Brandochili/Easy-Shot/20240221_093328.jpg

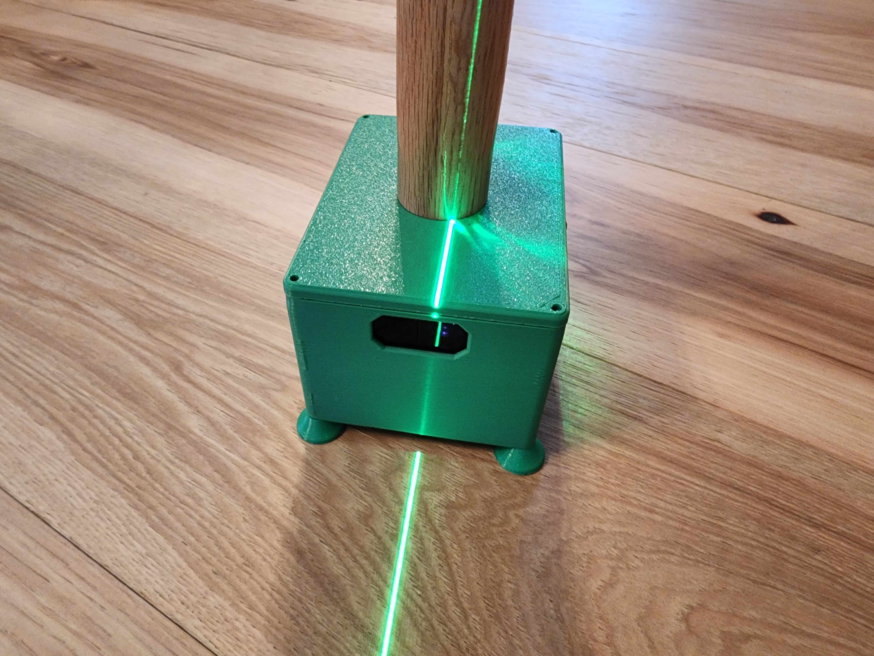
20240221_093328.jpg
