Brandochili/Easy-Shot/20240221_093351.jpg

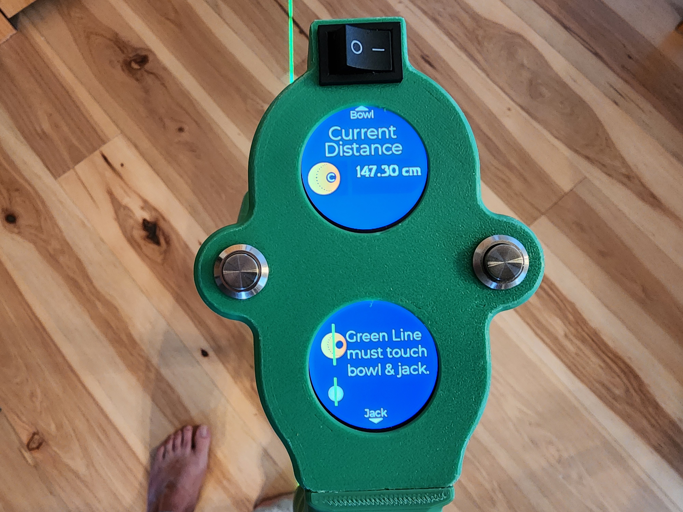
20240221_093351.jpg
