Brandochili/Easy-Shot/dial.h

const uint8_t dial[] PROGMEM = {
0xFF, 0xD8, 0xFF, 0xE0, 0x00, 0x10, 0x4A, 0x46, 0x49, 0x46, 0x00, 0x01, 0x02, 0x01, 0x00, 0x48, 
0x00, 0x48, 0x00, 0x00, 0xFF, 0xED, 0x00, 0x2C, 0x50, 0x68, 0x6F, 0x74, 0x6F, 0x73, 0x68, 0x6F, 
0x70, 0x20, 0x33, 0x2E, 0x30, 0x00, 0x38, 0x42, 0x49, 0x4D, 0x03, 0xED, 0x00, 0x00, 0x00, 0x00, 
0x00, 0x10, 0x00, 0x48, 0x00, 0x00, 0x00, 0x01, 0x00, 0x01, 0x00, 0x48, 0x00, 0x00, 0x00, 0x01, 
0x00, 0x01, 0xFF, 0xE1, 0x7E, 0xFE, 0x68, 0x74, 0x74, 0x70, 0x3A, 0x2F, 0x2F, 0x6E, 0x73, 0x2E, 
0x61, 0x64, 0x6F, 0x62, 0x65, 0x2E, 0x63, 0x6F, 0x6D, 0x2F, 0x78, 0x61, 0x70, 0x2F, 0x31, 0x2E, 
0x30, 0x2F, 0x00, 0x3C, 0x3F, 0x78, 0x70, 0x61, 0x63, 0x6B, 0x65, 0x74, 0x20, 0x62, 0x65, 0x67, 
0x69, 0x6E, 0x3D, 0x22, 0xEF, 0xBB, 0xBF, 0x22, 0x20, 0x69, 0x64, 0x3D, 0x22, 0x57, 0x35, 0x4D, 
0x30, 0x4D, 0x70, 0x43, 0x65, 0x68, 0x69, 0x48, 0x7A, 0x72, 0x65, 0x53, 0x7A, 0x4E, 0x54, 0x63, 
0x7A, 0x6B, 0x63, 0x39, 0x64, 0x22, 0x3F, 0x3E, 0x0A, 0x3C, 0x78, 0x3A, 0x78, 0x6D, 0x70, 0x6D, 
0x65, 0x74, 0x61, 0x20, 0x78, 0x6D, 0x6C, 0x6E, 0x73, 0x3A, 0x78, 0x3D, 0x22, 0x61, 0x64, 0x6F, 
0x62, 0x65, 0x3A, 0x6E, 0x73, 0x3A, 0x6D, 0x65, 0x74, 0x61, 0x2F, 0x22, 0x20, 0x78, 0x3A, 0x78, 
0x6D, 0x70, 0x74, 0x6B, 0x3D, 0x22, 0x41, 0x64, 0x6F, 0x62, 0x65, 0x20, 0x58, 0x4D, 0x50, 0x20, 
0x43, 0x6F, 0x72, 0x65, 0x20, 0x39, 0x2E, 0x30, 0x2D, 0x63, 0x30, 0x30, 0x31, 0x20, 0x37, 0x39, 
0x2E, 0x31, 0x34, 0x65, 0x63, 0x62, 0x34, 0x32, 0x2C, 0x20, 0x32, 0x30, 0x32, 0x32, 0x2F, 0x31, 
0x32, 0x2F, 0x30, 0x32, 0x2D, 0x31, 0x39, 0x3A, 0x31, 0x32, 0x3A, 0x34, 0x34, 0x20, 0x20, 0x20, 
0x20, 0x20, 0x20, 0x20, 0x20, 0x22, 0x3E, 0x0A, 0x20, 0x20, 0x20, 0x3C, 0x72, 0x64, 0x66, 0x3A, 
0x52, 0x44, 0x46, 0x20, 0x78, 0x6D, 0x6C, 0x6E, 0x73, 0x3A, 0x72, 0x64, 0x66, 0x3D, 0x22, 0x68, 
0x74, 0x74, 0x70, 0x3A, 0x2F, 0x2F, 0x77, 0x77, 0x77, 0x2E, 0x77, 0x33, 0x2E, 0x6F, 0x72, 0x67, 
0x2F, 0x31, 0x39, 0x39, 0x39, 0x2F, 0x30, 0x32, 0x2F, 0x32, 0x32, 0x2D, 0x72, 0x64, 0x66, 0x2D, 
0x73, 0x79, 0x6E, 0x74, 0x61, 0x78, 0x2D, 0x6E, 0x73, 0x23, 0x22, 0x3E, 0x0A, 0x20, 0x20, 0x20, 
0x20, 0x20, 0x20, 0x3C, 0x72, 0x64, 0x66, 0x3A, 0x44, 0x65, 0x73, 0x63, 0x72, 0x69, 0x70, 0x74, 
0x69, 0x6F, 0x6E, 0x20, 0x72, 0x64, 0x66, 0x3A, 0x61, 0x62, 0x6F, 0x75, 0x74, 0x3D, 0x22, 0x22, 
0x0A, 0x20, 0x20, 0x20, 0x20, 0x20, 0x20, 0x20, 0x20, 0x20, 0x20, 0x20, 0x20, 0x78, 0x6D, 0x6C, 
0x6E, 0x73, 0x3A, 0x64, 0x63, 0x3D, 0x22, 0x68, 0x74, 0x74, 0x70, 0x3A, 0x2F, 0x2F, 0x70, 0x75, 
0x72, 0x6C, 0x2E, 0x6F, 0x72, 0x67, 0x2F, 0x64, 0x63, 0x2F, 0x65, 0x6C, 0x65, 0x6D, 0x65, 0x6E, 
0x74, 0x73, 0x2F, 0x31, 0x2E, 0x31, 0x2F, 0x22, 0x0A, 0x20, 0x20, 0x20, 0x20, 0x20, 0x20, 0x20, 
0x20, 0x20, 0x20, 0x20, 0x20, 0x78, 0x6D, 0x6C, 0x6E, 0x73, 0x3A, 0x78, 0x6D, 0x70, 0x3D, 0x22, 
0x68, 0x74, 0x74, 0x70, 0x3A, 0x2F, 0x2F, 0x6E, 0x73, 0x2E, 0x61, 0x64, 0x6F, 0x62, 0x65, 0x2E, 
0x63, 0x6F, 0x6D, 0x2F, 0x78, 0x61, 0x70, 0x2F, 0x31, 0x2E, 0x30, 0x2F, 0x22, 0x0A, 0x20, 0x20, 
0x20, 0x20, 0x20, 0x20, 0x20, 0x20, 0x20, 0x20, 0x20, 0x20, 0x78, 0x6D, 0x6C, 0x6E, 0x73, 0x3A, 
0x78, 0x6D, 0x70, 0x47, 0x49, 0x6D, 0x67, 0x3D, 0x22, 0x68, 0x74, 0x74, 0x70, 0x3A, 0x2F, 0x2F, 
0x6E, 0x73, 0x2E, 0x61, 0x64, 0x6F, 0x62, 0x65, 0x2E, 0x63, 0x6F, 0x6D, 0x2F, 0x78, 0x61, 0x70, 
0x2F, 0x31, 0x2E, 0x30, 0x2F, 0x67, 0x2F, 0x69, 0x6D, 0x67, 0x2F, 0x22, 0x0A, 0x20, 0x20, 0x20, 
0x20, 0x20, 0x20, 0x20, 0x20, 0x20, 0x20, 0x20, 0x20, 0x78, 0x6D, 0x6C, 0x6E, 0x73, 0x3A, 0x78, 
0x6D, 0x70, 0x4D, 0x4D, 0x3D, 0x22, 0x68, 0x74, 0x74, 0x70, 0x3A, 0x2F, 0x2F, 0x6E, 0x73, 0x2E, 
0x61, 0x64, 0x6F, 0x62, 0x65, 0x2E, 0x63, 0x6F, 0x6D, 0x2F, 0x78, 0x61, 0x70, 0x2F, 0x31, 0x2E, 
0x30, 0x2F, 0x6D, 0x6D, 0x2F, 0x22, 0x0A, 0x20, 0x20, 0x20, 0x20, 0x20, 0x20, 0x20, 0x20, 0x20, 
0x20, 0x20, 0x20, 0x78, 0x6D, 0x6C, 0x6E, 0x73, 0x3A, 0x73, 0x74, 0x52, 0x65, 0x66, 0x3D, 0x22, 
0x68, 0x74, 0x74, 0x70, 0x3A, 0x2F, 0x2F, 0x6E, 0x73, 0x2E, 0x61, 0x64, 0x6F, 0x62, 0x65, 0x2E, 
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
};
