Brandochili/Easy-Shot/20230622_110132.jpg

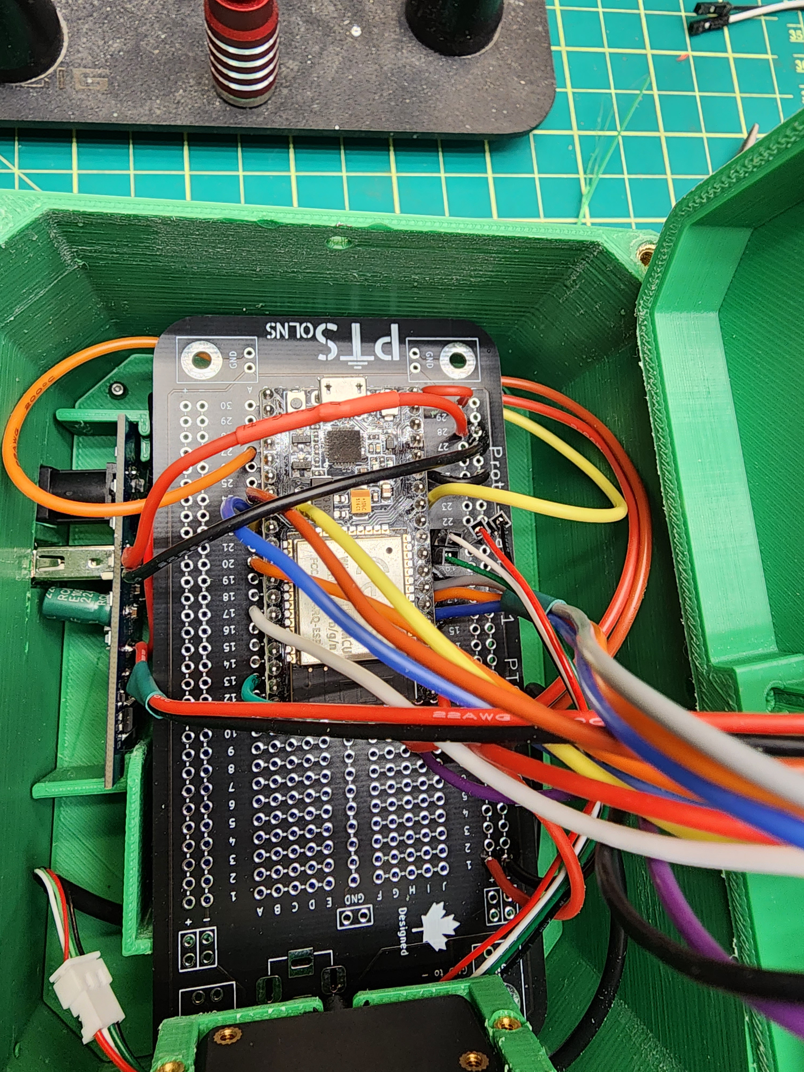
20230622_110132.jpg
