Brandochili/Easy-Shot/20230622_110135.jpg

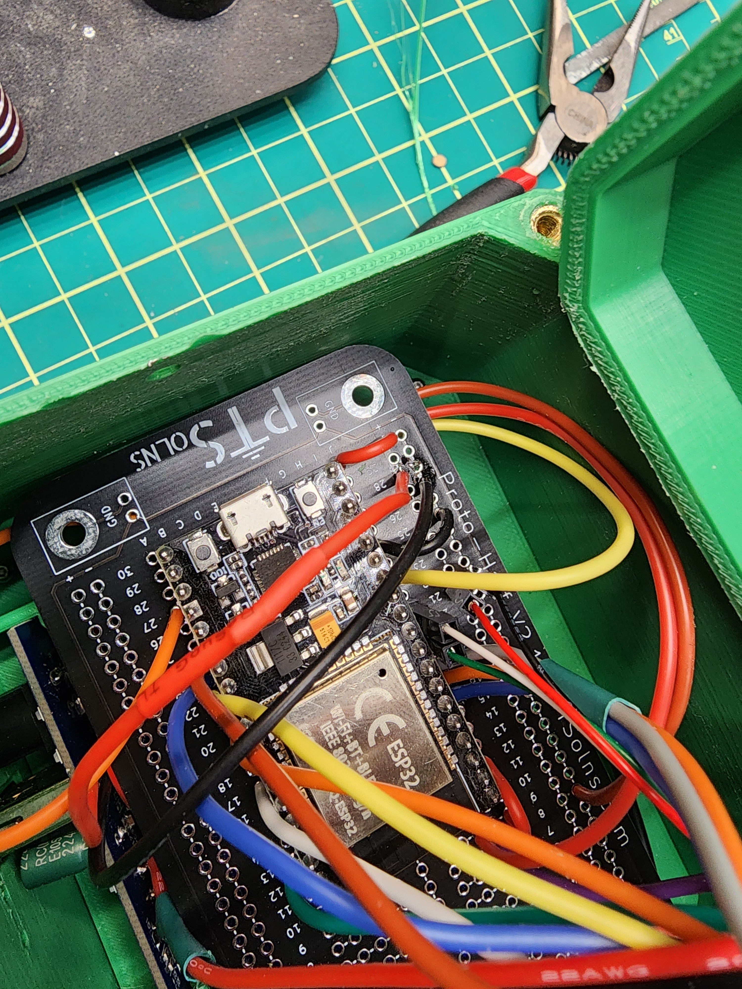
20230622_110135.jpg
