Brandochili/Easy-Shot/20240126_142008.jpg

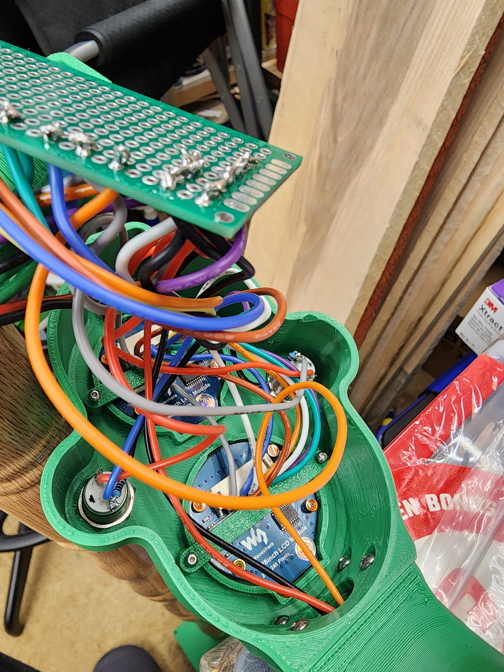
20240126_142008.jpg
